micked99/SX1278---APRS-balloon-tracker/main-v2/aprs.h

#ifndef APRS_H_
#define APRS_H_
#include <SPI.h>                                                                                   
#include <SX127XLT.h>
#include "config.h"
#define _1200   1
#define _2400   0
#define _FLAG       0x7e
#define _CTRL_ID    0x03
#define _PID        0xf0
#define _DT_EXP     ','
#define _DT_STATUS  '>'
#define _DT_POS     '!'
#define _FIXPOS         1
#define _STATUS         2
#define _FIXPOS_STATUS  3

// SX1278 hardware pin definitions 
#define NSS 5                                 
#define NRESET 7                                                               
#define DIO0 4                                 
#define DIO1 -1                               
#define DIO2 -1     

// use SX1278 radio module
#define LORA_DEVICE DEVICE_SX1278 
class aprs 
{

	public:

    aprs();
    ~aprs();
    SX127XLT* m_pSX1278; 

    void begin(void);
    
    String create_comment(int altitude, int aprs_packet_number, int gps_speed, int number_of_gps_satellites, String additional_comment);
  
		void send(String latitude, String longitude, String comment, float frequency);

	private:
    int w=1;
    int sx1278_tx_power = 16; // tx power in dbm, Softstart radio - begin with x dbm, 17 deafult, 20 max
		bool nada = _2400;
		const float baud_adj = 0.951;  // const float baud_adj = 0.975;  0.9634  0.952 med XO+tcxo
		const float adj_1200 = 1.0 * baud_adj;
		const float adj_2400 = 1.0 * baud_adj;
		unsigned int tc1200 = (unsigned int)(0.500 * adj_1200 * 1000000.0 / 1200.0);  //0.495
		unsigned int tc2400 = (unsigned int)(0.500 * adj_2400 * 1000000.0 / 2400.0);  //0.506
	  unsigned int str_len = 400;
		char bit_stuff = 0;
		unsigned short crc=0xffff;
		String mycall;
		char myssid;
		String dest;
		String digi;
		char digissid;
    char sym_ovl;
		char sym_tab;
    void set_nada_1200(void);
		void set_nada_2400(void);
		void set_nada(bool nada);
		void calc_crc(bool in_bit);
		void send_crc(void);
		void send_header(void);
		void send_payload_information(String comment, String latitude, String longitude);
		void send_char_NRZI(unsigned char in_byte, bool enBitStuff);
		void send_string_len(const char *in_string, int len);
		void send_flag(unsigned char flag_len);
		void randomize(unsigned int &var, unsigned int low, unsigned int high);

};

#endif /* APRS_H_ */
